mirkosertic/ESP32MusicBox/src/rfidplayermode.h

#ifndef RFIDPLAYERMODE_H
#define RFIDPLAYERMODE_H

#include "WiFiClient.h"
#include "app.h"
#include "bluetoothsource.h"
#include "mediaplayer.h"
#include "mode.h"
#include "mqtt.h"
#include "sdmediaplayersource.h"
#include "tagscanner.h"
#include "urlmediaplayersource.h"
#include "voiceassistant.h"
#include "webserver.h"

#include <AudioTools/AudioCodecs/CodecMP3Helix.h>
#include <AudioTools/Communication/HTTP/ICYStream.h>

class RfidPlayerMode : public Mode {
private:
	ICYStream *urlStream;
	Equalizer3Bands *equalizer;
	SDMediaPlayerSource *sourceSD;
	URLMediaPlayerSource *sourceURL;
	MP3DecoderHelix *decoder;
	MediaPlayer *player;
	TagScanner *tagscanner;
	App *app;
	WiFiClient *wifiClient;
	Webserver *webserver;
	MQTT *mqtt;
	VoiceAssistant *assistant;
	BufferRTOS<uint8_t> *buffer;
	QueueStream<uint8_t> *bluetoothout;
	BluetoothSource *bluetoothsource;
	PlaystateMonitor *playstatemonitor;
	QueueHandle_t commandsHandle;

	bool bluetoothSpeakerConnected;
	bool wifienabled;
	bool wifiinitialized;

	void wifiConnected();

public:
	RfidPlayerMode(Leds *leds, Sensors *sensors);

	virtual void setup() override;
	virtual ModeStatus loop() override;
	virtual void shutdown() override;
};

#endif
